gancaokuai/dorm-radar-pcb/firmware/arduino/rx/shared_libs.cpp

// Keeps the Arduino CLI build independent from custom library discovery.
#include "F:/DormRadar/firmware/lib/DormRadarProtocol/src/DormRadarProtocol.cpp"
#include "F:/DormRadar/firmware/lib/Ld2450/src/Ld2450.cpp"
